Ekam-wadhwa1/nexus.terminal/CAD FILES/STEP/COMPONENTS/USB C RECEPTACLE 14 PIN.step

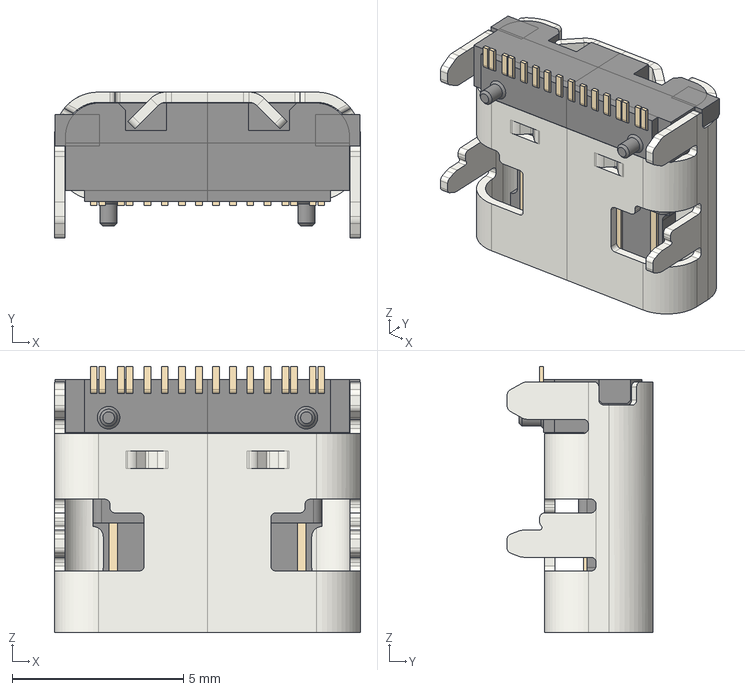
[picture p9: CAD file, 2026-07-17]
CAD FILES/STEP/COMPONENTS/USB C RECEPTACLE 14 PIN.step
8.94 x 4.26 x 7.78 mm
