Ekam-wadhwa1/nexus.terminal/CAD FILES/STEP/COMPONENTS/MX KEYSWITCH.step

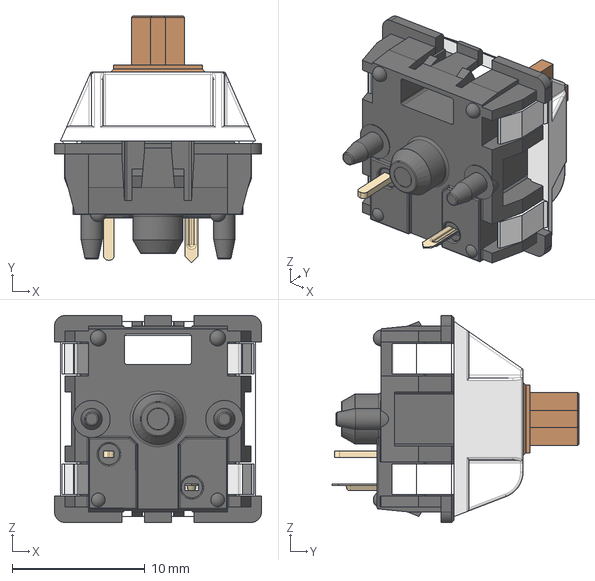
[picture p10: CAD file, 2026-07-17]
CAD FILES/STEP/COMPONENTS/MX KEYSWITCH.step
15.6 x 18.6 x 15.6 mm
