Ekam-wadhwa1/nexus.terminal/CAD FILES/STEP/COMPONENTS/Diode DO-35.step

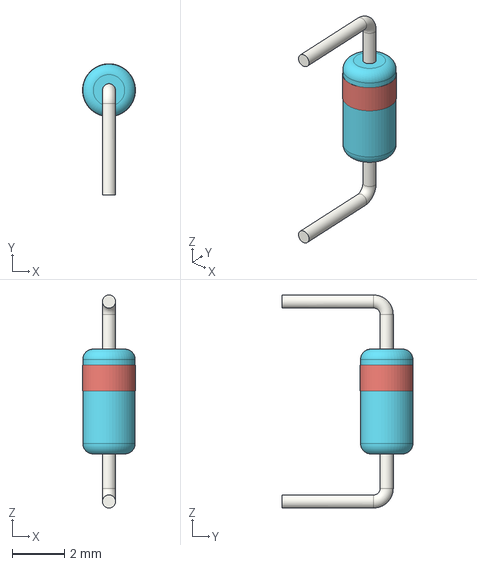
[picture p11: CAD file, 2026-07-17]
CAD FILES/STEP/COMPONENTS/Diode DO-35.step
2.02 x 5.01 x 8.12 mm
