Ekam-wadhwa1/nexus.terminal/KICAD FILES/KEYBOARD/KEYBOARD.kicad_sch

## KiCad design KICAD FILES/KEYBOARD/KEYBOARD.kicad_sch (2026-07-17)

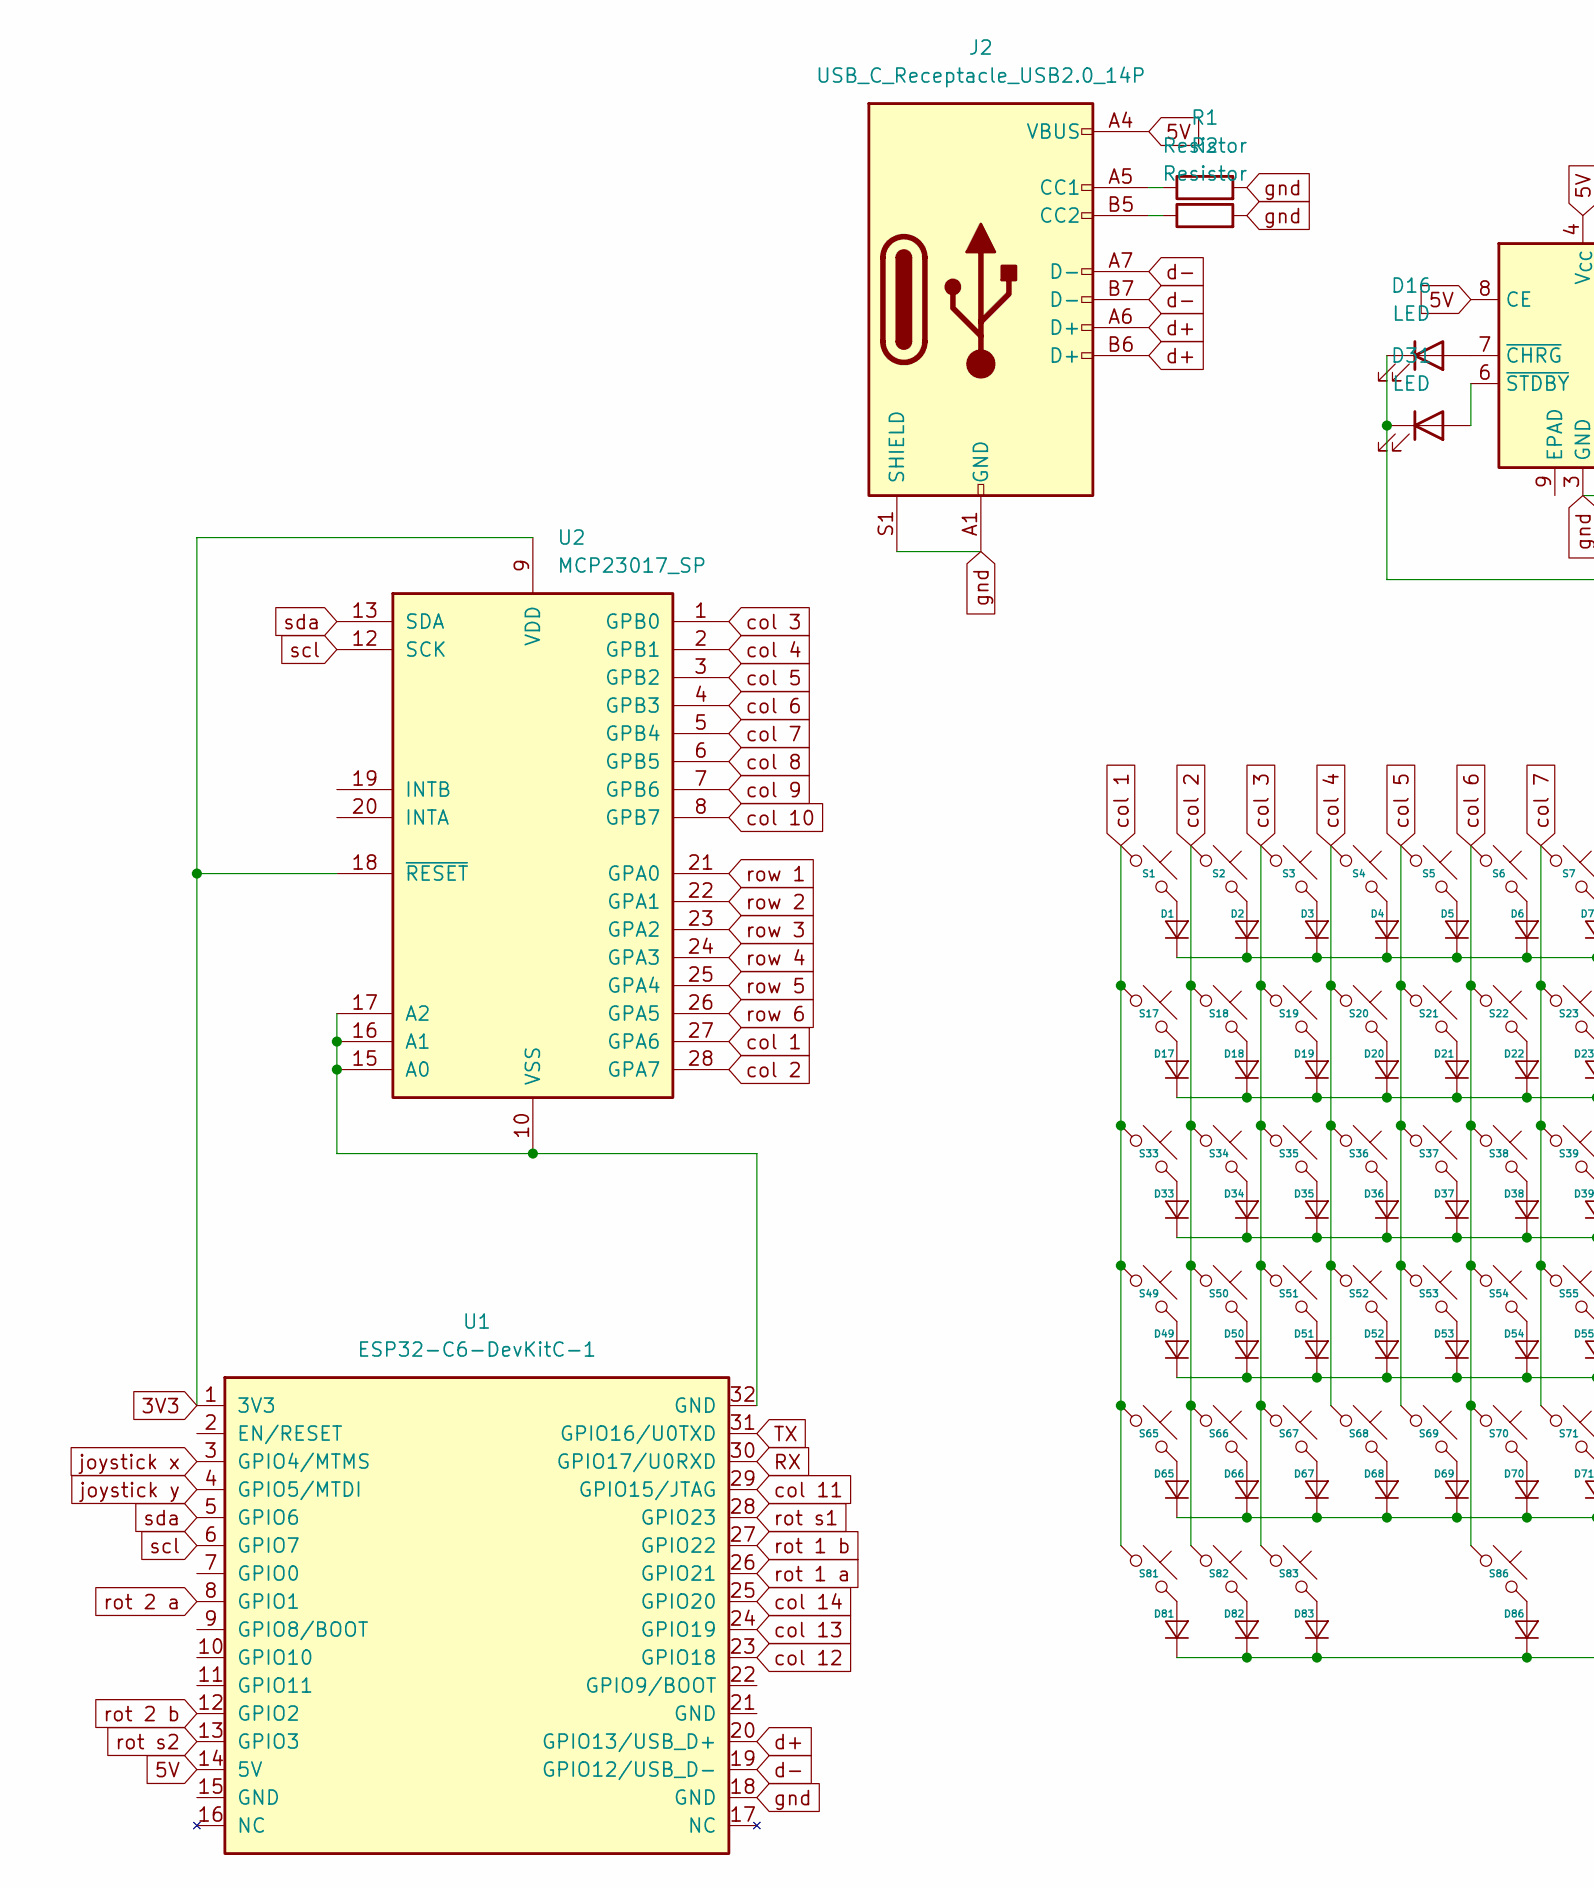
[picture p12: schematic KEYBOARD.kicad_sch, part in row 1, column 1]

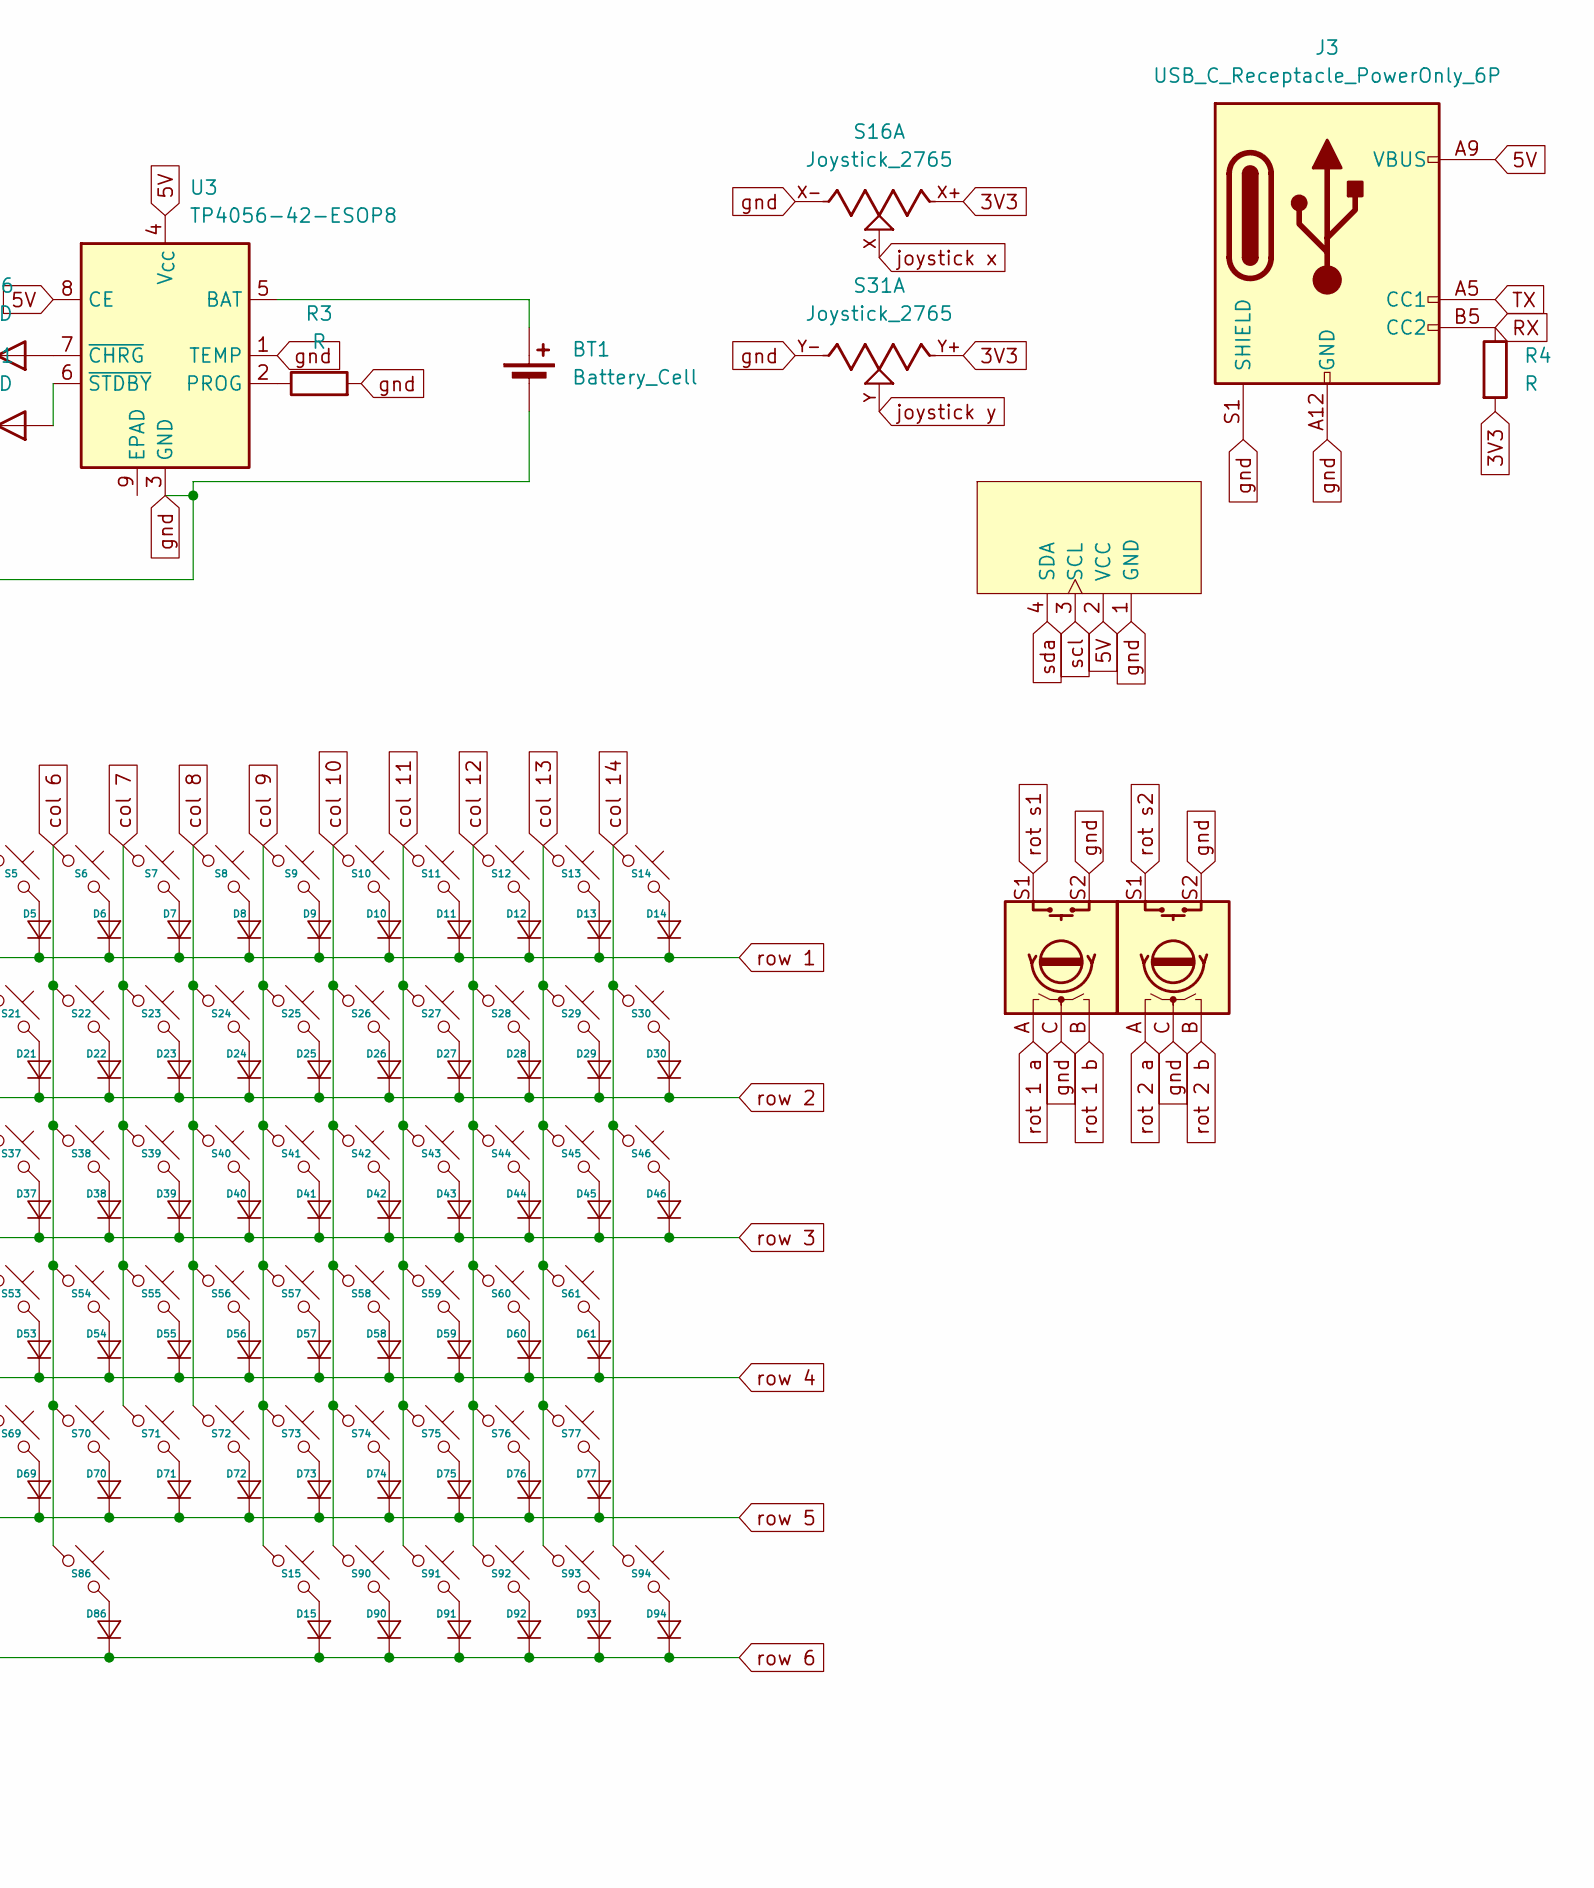
[picture p13: schematic KEYBOARD.kicad_sch, part in row 1, column 2]

Parts:
BT1: Battery_Cell; JST_PH_B2B-PH-K_1x02_P2.00mm_Vertical
D1, D2, D3, D4, D5, D6, D7, D8, D9, D10, D11, D12, D13, D14, D15, D17, D18, D19, D20, D21, D22, D23, D24, D25, D26, D27, D28, D29, D30, D33, D34, D35, D36, D37, D38, D39, D40, D41, D42, D43, D44, D45, D46, D49, D50, D51, D52, D53, D54, D55, D56, D57, D58, D59, D60, D61, D65, D66, D67, D68, D69, D70, D71, D72, D73, D74, D75, D76, D77, D81, D82, D83, D86, D90, D91, D92, D93, D94: Diode_DO-35
D16, D31: LED; LED_D3.0mm_Horizontal_O1.27mm_Z10.0mm
J1: OLED_128x64
J2: USB_C_Receptacle_USB2.0_14P; USB_C_Receptacle_GCT_USB4105-xx-A_16P_TopMnt_Horizontal
J3: USB_C_Receptacle_PowerOnly_6P; USB_C_Receptacle_GCT_USB4125-xx-x_6P_TopMnt_Horizontal
R1, R2: Resistor; R_Axial_DIN0204_L3.6mm_D1.6mm_P5.08mm_Horizontal
R3, R4: R; R_Axial_DIN0204_L3.6mm_D1.6mm_P5.08mm_Horizontal
S1, S2, S3, S4, S5, S6, S7, S8, S9, S10, S11, S12, S13, S14, S15, S17, S18, S19, S20, S21, S22, S23, S24, S25, S26, S27, S28, S29, S34, S35, S36, S37, S38, S39, S40, S41, S42, S43, S44, S45, S50, S51, S52, S53, S54, S55, S56, S57, S58, S59, S60, S66, S67, S68, S69, S70, S71, S72, S73, S74, S75, S77, S90, S91, S92, S93, S94: MX_PCB_1.00u
S16, S31: Joystick_2765
S30: MX_PCB_2.00u
S33, S46: MX_PCB_1.50u
S49, S76: MX_PCB_1.75u
S61, S65: MX_PCB_2.25u
S81, S82, S83: MX_PCB_1.25u
S86: MX_PCB_6.25u
SW1, SW2: RotaryEncoder_Switch; RotaryEncoder_Alps_EC12E-Switch_Vertical_H20mm_CircularMoun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
U1: ESP32-C6-DevKitC-1
U2: MCP23017_SP; DIP-28_W7.62mm
U3: TP4056-42-ESOP8; SOIC-8-1EP_3.9x4.9mm_P1.27mm_EP2.41x3.3mm_ThermalVias

Connections:
3V3: R4.2, S16.X+, S31.Y+, U1.1 (3V3), U2.9 (VDD), U2.18 (~RESET)
5V: J1.2 (VCC), J2.A4 (VBUS), J2.A9 (VBUS), J2.B4 (VBUS), J2.B9 (VBUS), J3.A9 (VBUS), J3.B9 (VBUS), U1.14 (5V), U3.4 (V_{CC}), U3.8 (CE)
unnamed: BT1.1 (+), U3.5 (BAT)
unnamed: D1.2 (A), S1.2
unnamed: D2.2 (A), S2.2
unnamed: D3.2 (A), S3.2
unnamed: D4.2 (A), S4.2
unnamed: D5.2 (A), S5.2
unnamed: D6.2 (A), S6.2
unnamed: D7.2 (A), S7.2
unnamed: D8.2 (A), S8.2
unnamed: D9.2 (A), S9.2
unnamed: D10.2 (A), S10.2
unnamed: D11.2 (A), S11.2
unnamed: D12.2 (A), S12.2
unnamed: D13.2 (A), S13.2
unnamed: D14.2 (A), S14.2
unnamed: D15.2 (A), S15.2
unnamed: D16.2 (A), U3.7 (~CHRG)
unnamed: D17.2 (A), S17.2
unnamed: D18.2 (A), S18.2
unnamed: D19.2 (A), S19.2
unnamed: D20.2 (A), S20.2
unnamed: D21.2 (A), S21.2
unnamed: D22.2 (A), S22.2
unnamed: D23.2 (A), S23.2
unnamed: D24.2 (A), S24.2
unnamed: D25.2 (A), S25.2
unnamed: D26.2 (A), S26.2
unnamed: D27.2 (A), S27.2
unnamed: D28.2 (A), S28.2
unnamed: D29.2 (A), S29.2
unnamed: D30.2 (A), S30.2
unnamed: D31.2 (A), U3.6 (~STDBY)
unnamed: D33.2 (A), S33.2
unnamed: D34.2 (A), S34.2
unnamed: D35.2 (A), S35.2
unnamed: D36.2 (A), S36.2
unnamed: D37.2 (A), S37.2
unnamed: D38.2 (A), S38.2
unnamed: D39.2 (A), S39.2
unnamed: D40.2 (A), S40.2
unnamed: D41.2 (A), S41.2
unnamed: D42.2 (A), S42.2
unnamed: D43.2 (A), S43.2
unnamed: D44.2 (A), S44.2
unnamed: D45.2 (A), S45.2
unnamed: D46.2 (A), S46.2
unnamed: D49.2 (A), S49.2
unnamed: D50.2 (A), S50.2
unnamed: D51.2 (A), S51.2
unnamed: D52.2 (A), S52.2
unnamed: D53.2 (A), S53.2
unnamed: D54.2 (A), S54.2
unnamed: D55.2 (A), S55.2
unnamed: D56.2 (A), S56.2
unnamed: D57.2 (A), S57.2
unnamed: D58.2 (A), S58.2
unnamed: D59.2 (A), S59.2
unnamed: D60.2 (A), S60.2
unnamed: D61.2 (A), S61.2
unnamed: D65.2 (A), S65.2
unnamed: D66.2 (A), S66.2
unnamed: D67.2 (A), S67.2
unnamed: D68.2 (A), S68.2
unnamed: D69.2 (A), S69.2
unnamed: D70.2 (A), S70.2
unnamed: D71.2 (A), S71.2
unnamed: D72.2 (A), S72.2
unnamed: D73.2 (A), S73.2
unnamed: D74.2 (A), S74.2
unnamed: D75.2 (A), S75.2
unnamed: D76.2 (A), S76.2
unnamed: D77.2 (A), S77.2
unnamed: D81.2 (A), S81.2
unnamed: D82.2 (A), S82.2
unnamed: D83.2 (A), S83.2
unnamed: D86.2 (A), S86.2
unnamed: D90.2 (A), S90.2
unnamed: D91.2 (A), S91.2
unnamed: D92.2 (A), S92.2
unnamed: D93.2 (A), S93.2
unnamed: D94.2 (A), S94.2
unnamed: J2.A5 (CC1), R1.1
unnamed: J2.B5 (CC2), R2.1
unnamed: R3.1, U3.2 (PROG)
unnamed: U1.32 (GND), U2.10 (VSS), U2.15 (A0), U2.16 (A1), U2.17 (A2)
RX: J3.B5 (CC2), R4.1, U1.30 (GPIO17/U0RXD)
TX: J3.A5 (CC1), U1.31 (GPIO16/U0TXD)
col 1: S1.1, S17.1, S33.1, S49.1, S65.1, S81.1, U2.27 (GPA6)
col 2: S2.1, S18.1, S34.1, S50.1, S66.1, S82.1, U2.28 (GPA7)
col 3: S3.1, S19.1, S35.1, S51.1, S67.1, S83.1, U2.1 (GPB0)
col 4: S4.1, S20.1, S36.1, S52.1, S68.1, U2.2 (GPB1)
col 5: S5.1, S21.1, S37.1, S53.1, S69.1, U2.3 (GPB2)
col 6: S6.1, S22.1, S38.1, S54.1, S70.1, S86.1, U2.4 (GPB3)
col 7: S7.1, S23.1, S39.1, S55.1, S71.1, U2.5 (GPB4)
col 8: S8.1, S24.1, S40.1, S56.1, S72.1, U2.6 (GPB5)
col 9: S9.1, S15.1, S25.1, S41.1, S57.1, S73.1, U2.7 (GPB6)
col 10: S10.1, S26.1, S42.1, S58.1, S74.1, S90.1, U2.8 (GPB7)
col 11: S11.1, S27.1, S43.1, S59.1, S75.1, S91.1, U1.29 (GPIO15/JTAG)
col 12: S12.1, S28.1, S44.1, S60.1, S76.1, S92.1, U1.23 (GPIO18)
col 13: S13.1, S29.1, S45.1, S61.1, S77.1, S93.1, U1.24 (GPIO19)
col 14: S14.1, S30.1, S46.1, S94.1, U1.25 (GPIO20)
d+: J2.A6 (D+), J2.B6 (D+), U1.20 (GPIO13/USB_D+)
d-: J2.A7 (D-), J2.B7 (D-), U1.19 (GPIO12/USB_D-)
gnd: BT1.2 (-), D16.1 (K), D31.1 (K), J1.1 (GND), J2.A1 (GND), J2.A12 (GND), J2.B1 (GND), J2.B12 (GND), J2.S1 (SHIELD), J3.A12 (GND), J3.B12 (GND), J3.S1 (SHIELD), R1.2, R2.2, R3.2, S16.X-, S31.Y-, SW1.C, SW1.S2, SW2.C, SW2.S2, U1.18 (GND), U3.1 (TEMP), U3.3 (GND)
joystick x: S16.X, U1.3 (GPIO4/MTMS)
joystick y: S31.Y, U1.4 (GPIO5/MTDI)
rot 1 a: SW1.A, U1.26 (GPIO21)
rot 1 b: SW1.B, U1.27 (GPIO22)
rot 2 a: SW2.A, U1.8 (GPIO1)
rot 2 b: SW2.B, U1.12 (GPIO2)
rot s1: SW1.S1, U1.28 (GPIO23)
rot s2: SW2.S1, U1.13 (GPIO3)
row 1: D1.1 (K), D2.1 (K), D3.1 (K), D4.1 (K), D5.1 (K), D6.1 (K), D7.1 (K), D8.1 (K), D9.1 (K), D10.1 (K), D11.1 (K), D12.1 (K), D13.1 (K), D14.1 (K), U2.21 (GPA0)
row 2: D17.1 (K), D18.1 (K), D19.1 (K), D20.1 (K), D21.1 (K), D22.1 (K), D23.1 (K), D24.1 (K), D25.1 (K), D26.1 (K), D27.1 (K), D28.1 (K), D29.1 (K), D30.1 (K), U2.22 (GPA1)
row 3: D33.1 (K), D34.1 (K), D35.1 (K), D36.1 (K), D37.1 (K), D38.1 (K), D39.1 (K), D40.1 (K), D41.1 (K), D42.1 (K), D43.1 (K), D44.1 (K), D45.1 (K), D46.1 (K), U2.23 (GPA2)
row 4: D49.1 (K), D50.1 (K), D51.1 (K), D52.1 (K), D53.1 (K), D54.1 (K), D55.1 (K), D56.1 (K), D57.1 (K), D58.1 (K), D59.1 (K), D60.1 (K), D61.1 (K), U2.24 (GPA3)
row 5: D65.1 (K), D66.1 (K), D67.1 (K), D68.1 (K), D69.1 (K), D70.1 (K), D71.1 (K), D72.1 (K), D73.1 (K), D74.1 (K), D75.1 (K), D76.1 (K), D77.1 (K), U2.25 (GPA4)
row 6: D15.1 (K), D81.1 (K), D82.1 (K), D83.1 (K), D86.1 (K), D90.1 (K), D91.1 (K), D92.1 (K), D93.1 (K), D94.1 (K), U2.26 (GPA5)
scl: J1.3 (SCL), U1.6 (GPIO7), U2.12 (SCK)
sda: J1.4 (SDA), U1.5 (GPIO6), U2.13 (SDA)
